OLIMEX/ESP32-POE/SOFTWARE/ARDUINO/ESP32-OTA-Ethernet-web-server/Update-progress-and-auto-recovery.jpg

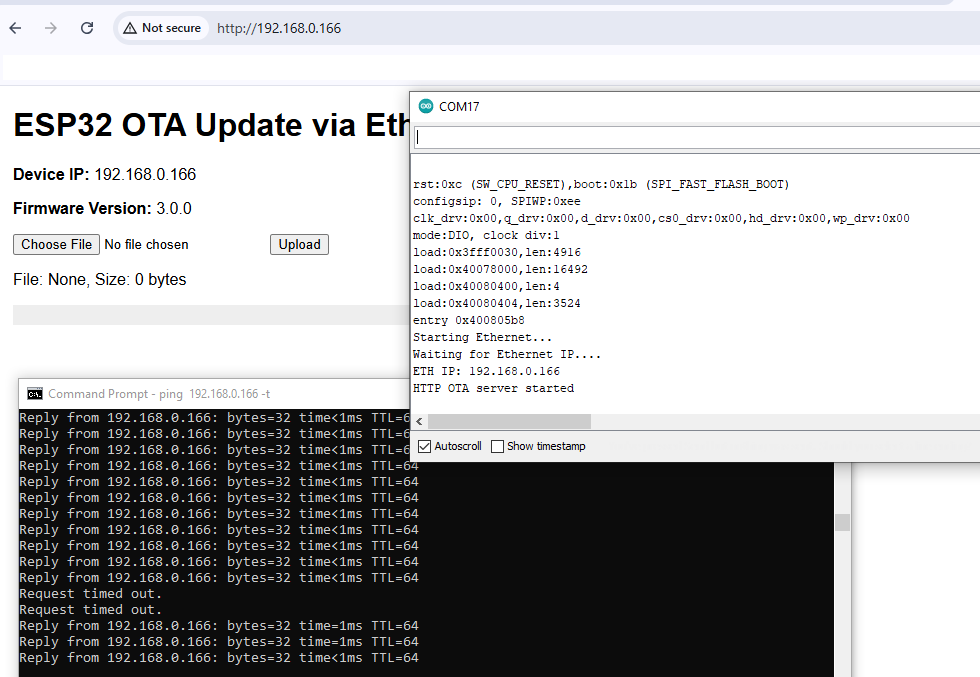
SOFTWARE/ARDUINO/ESP32-OTA-Ethernet-web-server/Update-progress-and-auto-recovery.jpg
