OLIMEX/ESP32-POE/HARDWARE/ESP32-PoE-hardware-revision-L1/3d/Micro_SD_card.step

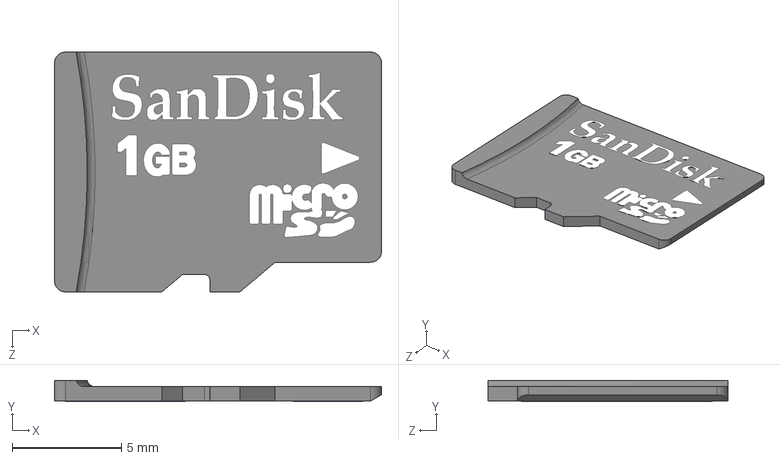
[picture p26: CAD file, 2019-03-11]
HARDWARE/ESP32-PoE-hardware-revision-L1/3d/Micro_SD_card.step
15.0 x 0.975 x 11.0 mm
