OLIMEX/ESP32-POE/HARDWARE/ESP32-PoE-hardware-revision-D/3d/CD32_inductor.step

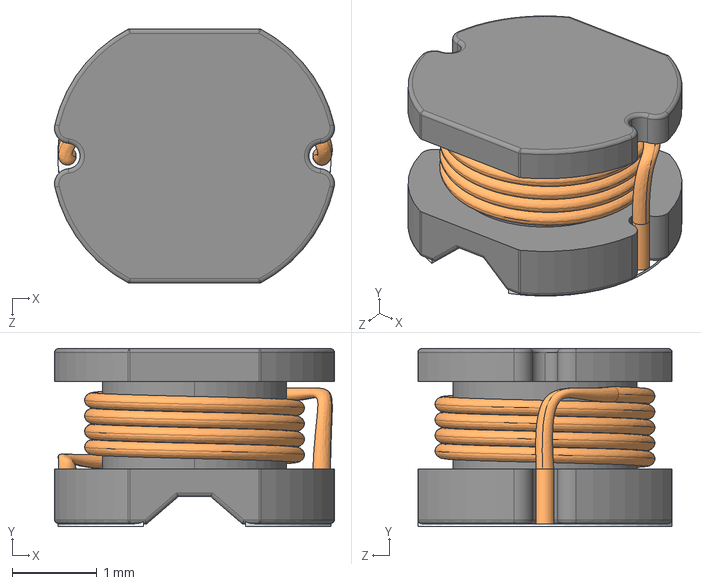
[picture p27: CAD file, 2019-03-11, an earlier design]
HARDWARE/ESP32-PoE-hardware-revision-D/3d/CD32_inductor.step
3.30 x 2.10 x 3.00 mm
