OLIMEX/ESP32-POE/SOFTWARE/ARDUINO/ESP32-BME280-WEB/ESP32-BME280-advanced/example-result.jpg

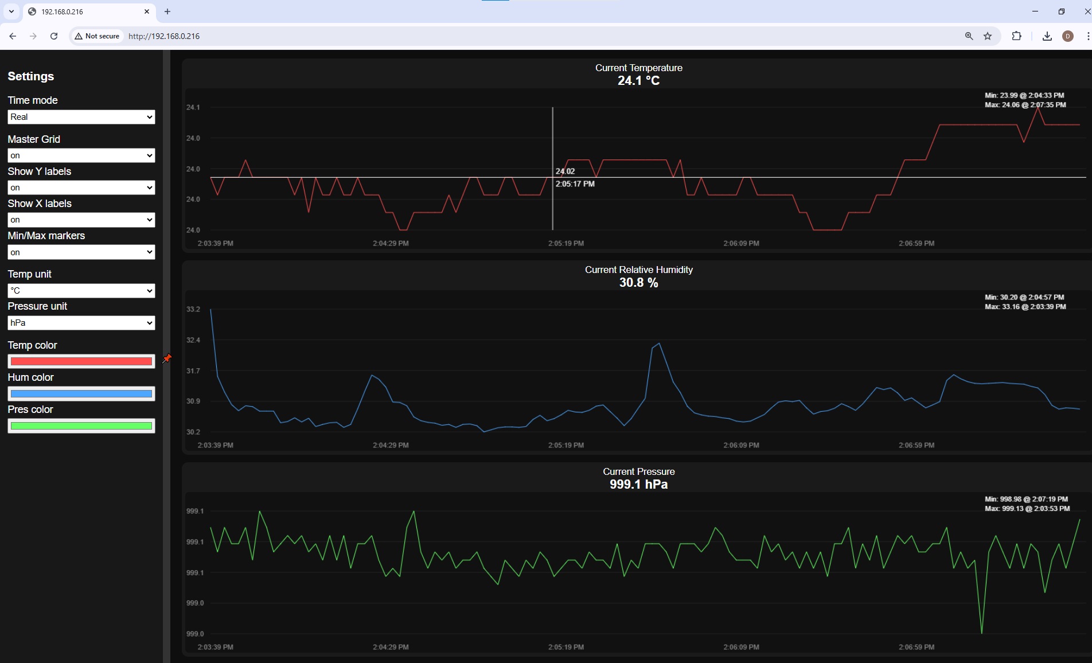
SOFTWARE/ARDUINO/ESP32-BME280-WEB/ESP32-BME280-advanced/example-result.jpg
