OLIMEX/ESP32-POE/SOFTWARE/ARDUINO/ESP32-BME280-WEB/ESP32-BME280-simple/example-result.jpg

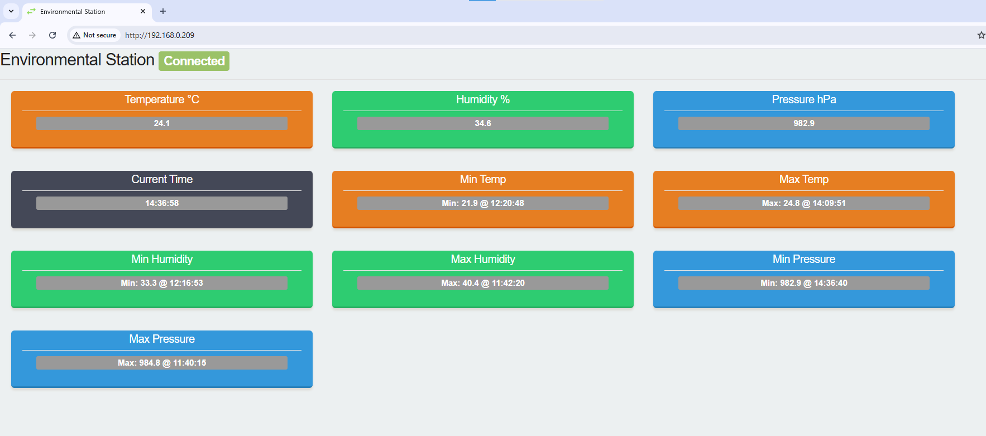
SOFTWARE/ARDUINO/ESP32-BME280-WEB/ESP32-BME280-simple/example-result.jpg
