OLIMEX/ESP32-POE/HARDWARE/ESP32-PoE-hardware-revision-J/ESP32-PoE_Rev_J.pdf

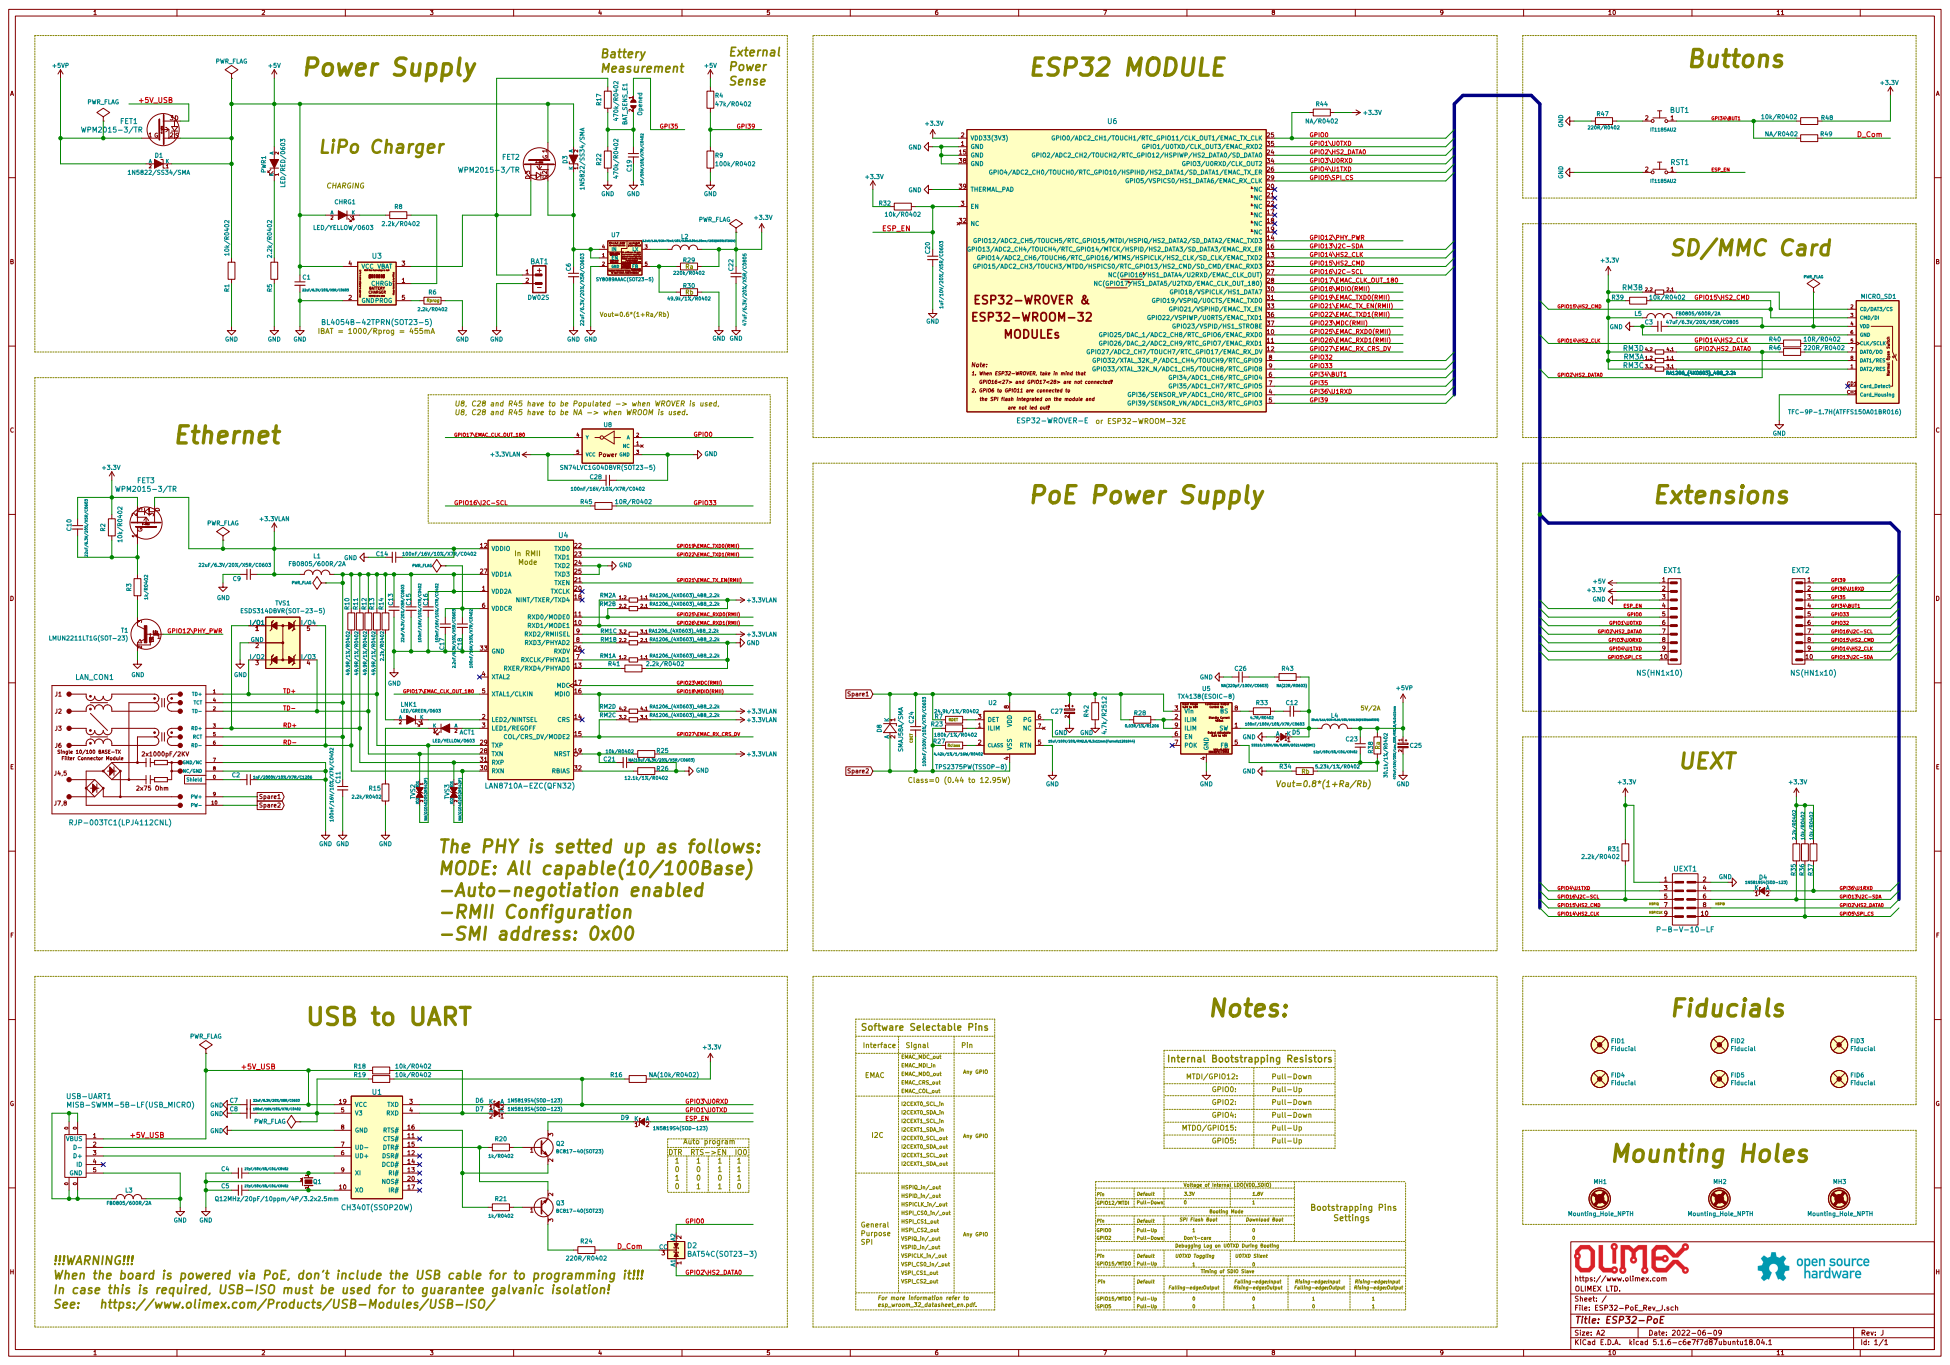
[picture p48: page 1]
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

load current capability! Lx=2.2uH
Cout=2x22uF/6.3V/X5R DCR<50mR

SD/MMC Card Ra Rb
GPIO15\HS2_CMD GPIO16\I2C-SCL GPIO13\I2C-SDA

Vout=0.6*(1+Ra/Rb) EN 1 GND 2

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

1. 1. 1. When ESP32-WROVER, take in mind that

GPIO16<27> and GPIO17<28> are not connected! MODULEs

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

4 RTN 5 PG 6 NC VDD 7 8U2 TPS2375PW(TSSOP-8) C15 100nF/16V/10%/X7R/C0402

2 D8 SMAJ58A/SMA IO11 IO22TVS3 NA(GG0402052R542P) IO11 IO22TVS2 NA(GG0402052R542P) GND

4 FB 5 EN 6 POK 7 BS 8

1 2 C25 470uF/10V/20%/Low_ESR/RM2.5/6.0x11mm ILIM 1 CLASS 2 DET 3 VSS

Default Default USB to UART

EMAC_MDC_out EMAC_MDI_in EMAC_MDO_out EMAC_CRS_out !!!WARNING!!! When the board is powered via PoE, don't include the USB cable for to programming it!!!

0 Falling-edge:Input GPIO15/MTDO

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

File: ESP32-PoE_Rev_J.sch Sheet: / OLIMEX LTD. https://www.olimex.com
