OLIMEX/ESP32-POE/HARDWARE/ESP32-PoE-hardware-revision-I/ESP32-PoE_Rev_I_BOM.pdf

ESP32-PoE_Rev_I_BOM | 12/23/2021

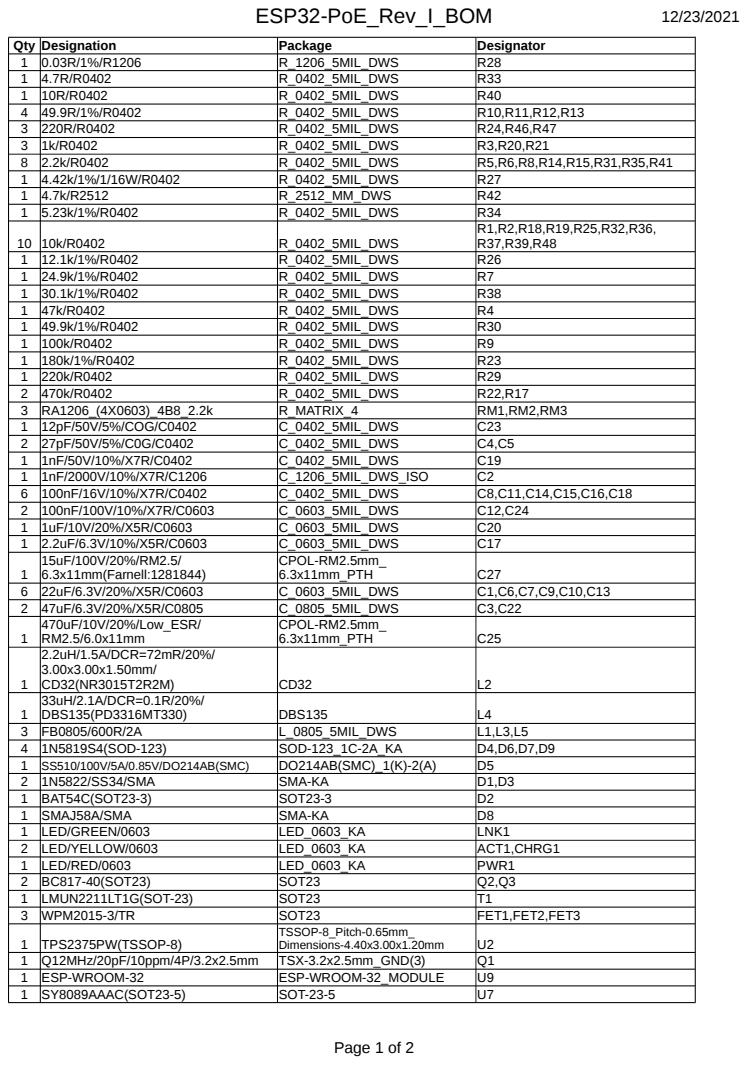
[picture p49: page 1]

ESP32-PoE_Rev_I_BOM | 12/23/2021
1 LAN8710A-EZC(QFN32) | | U4
1 BL4054B-42TPRN(SOT23-5) | SOT-23-5 | U3
1 CH340T(SSOP20W) | SSOP-20W | U1
1 TX4138(ESOIC-8) | ESOIC-8 | U5
1 ESDS314DBVR(SOT-23-5) | SOT-23-5 | TVS1
1 TFC-9P-1.7H(ATFFS150A01BR016) | | MICRO_SD1
1 RJP-003TC1(LPJ4112CNL) | RJP-003TC1(LPJ4112CNL) | LAN_CON1
1 DW02R | LIPO_BAT-CON2DW02R | BAT1
1 MISB-SWMM-5B-LF(USB_MICRO) | USB-MICRO_MISB-SWMM-5B_LF USB-UART1
1 P-B-V-10-LF | GBH-254-SMT-10 | UEXT1
2 NS(HN1x10) | HN1x10 | EXT2,EXT1
2 IT1185AU2 | IT1185AU2_V2 | BUT1,RST1
1 Opened | SJ_1_SMALLER | BAT_SENS_E1
2 NA(GG0402052R542P) | D_0402_5MIL_DWS | TVS2,TVS3
1 NA(10k/R0402) | R_0402_5MIL_DWS | R16
2 NA/R0402 | R_0402_5MIL_DWS | R44,R49
1 NA(10uF/6.3V/20%/X5R/C0603) | C_0603_5MIL_DWS | C21
1 NA(22R/R0603) | R_0603_5MIL_DWS | R43
1 NA(220pF/100V/C0603) | C_0603_5MIL_DWS | C26

QFN32_EP(33)_5.00x5.00x
0.90mm_Pitch_0.50mm

uSD(TFC-9P-1.xH
(ATFFS150A01BR016))
