OLIMEX/ESP32-POE/HARDWARE/ESP32-PoE-hardware-revision-G1/ESP32-PoE_Rev_G1.pdf

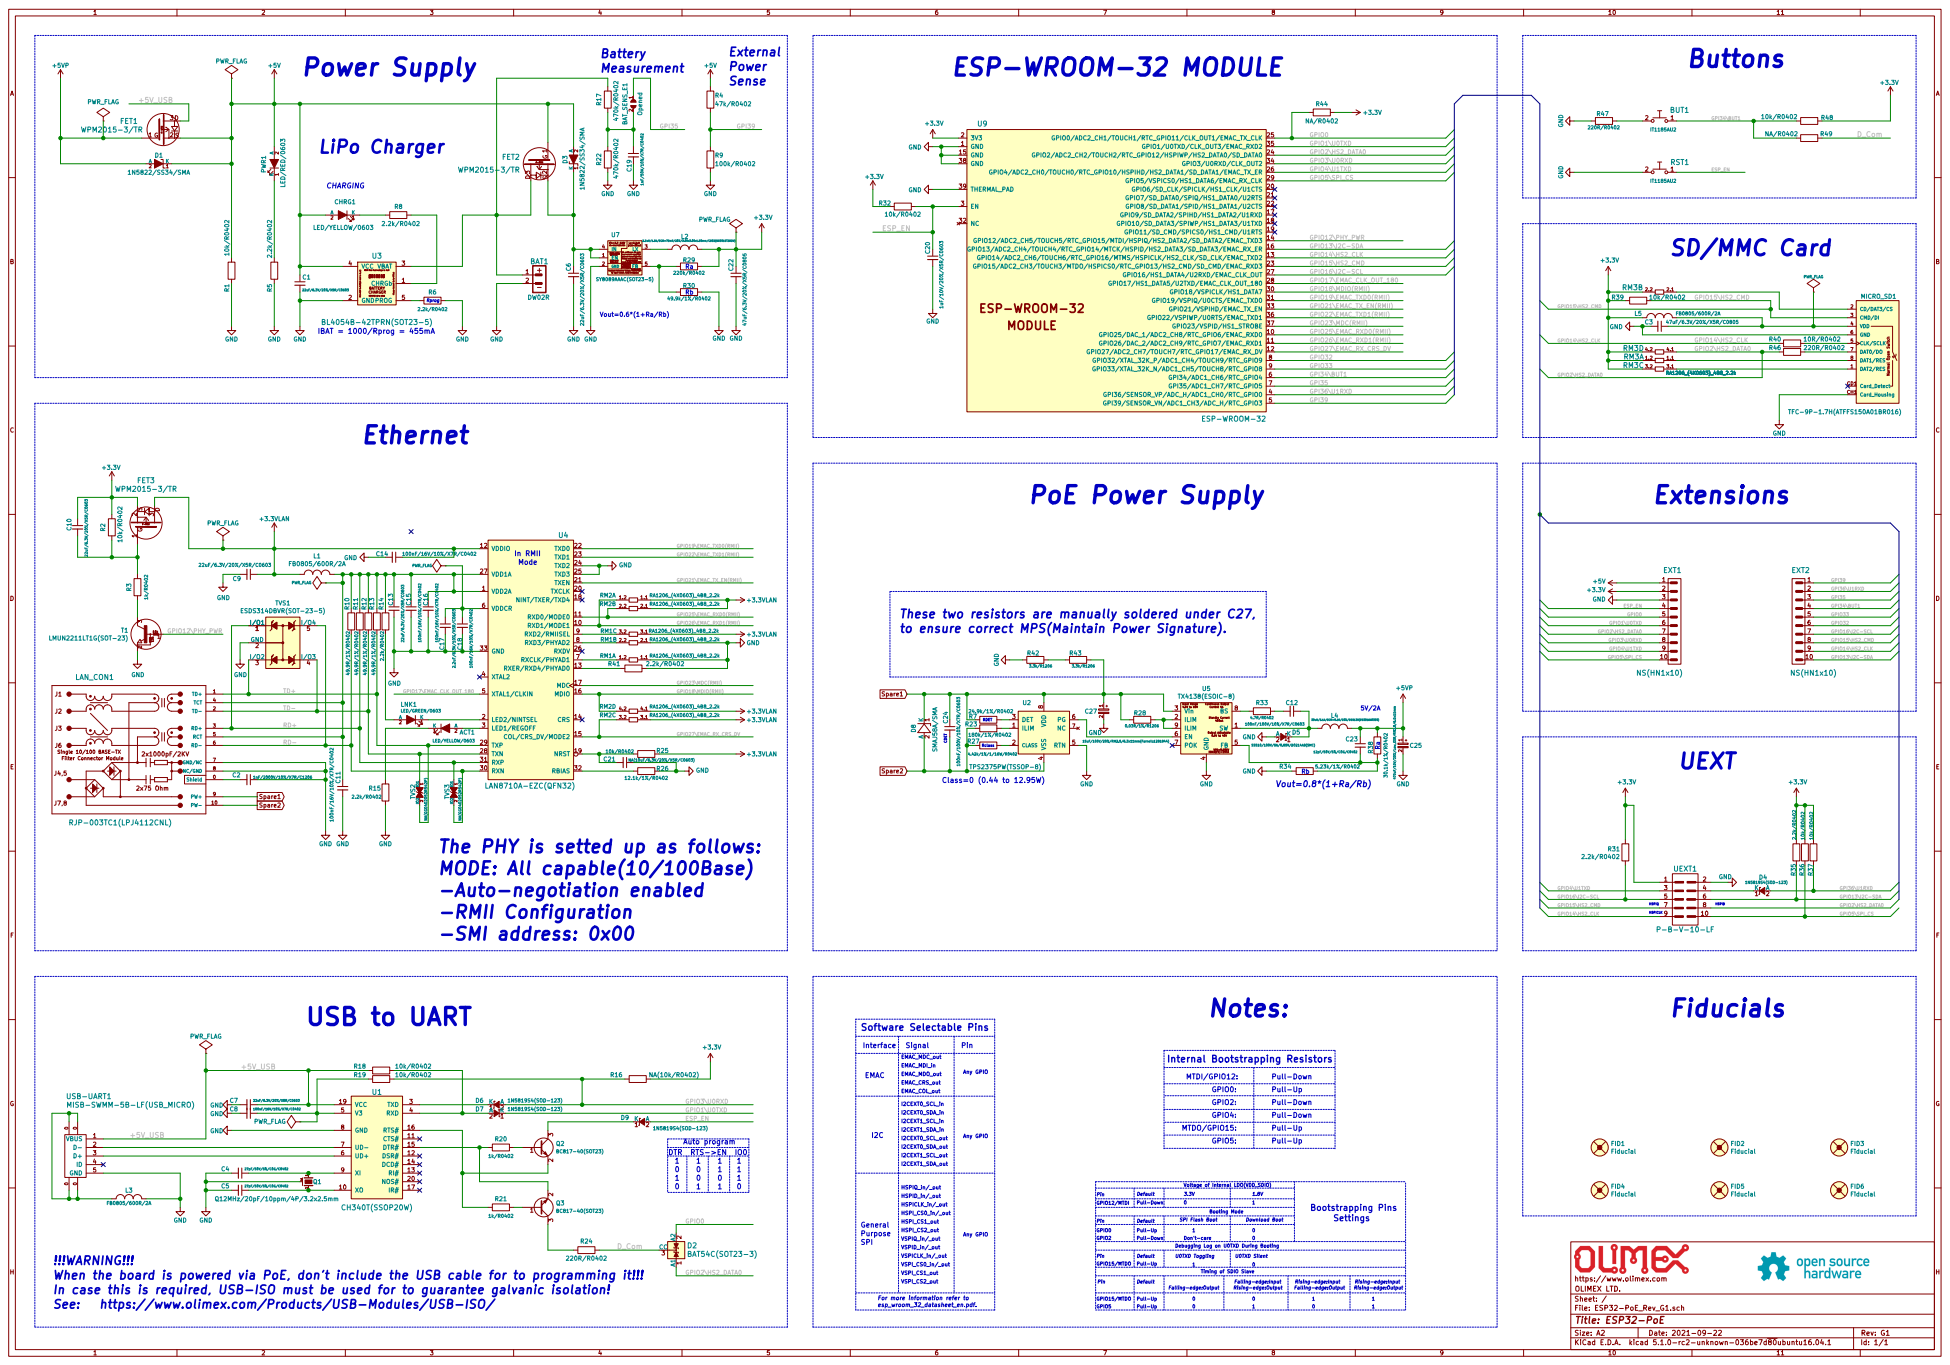
[picture p50: page 1]

load current capability! Lx=2.2uH

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

PWR_FLAG The PHY is setted up as follows:

to ensure correct MPS(Maintain Power Signature). R43

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

File: ESP32-PoE_Rev_G1.sch Sheet: / OLIMEX LTD. https://www.olimex.com
