OLIMEX/ESP32-POE/HARDWARE/ESP32-PoE-hardware-revision-G1/ESP32-PoE_Rev_G1_BOM.pdf

ESP32-PoE_Rev_G1_BOM | 11/05/2021

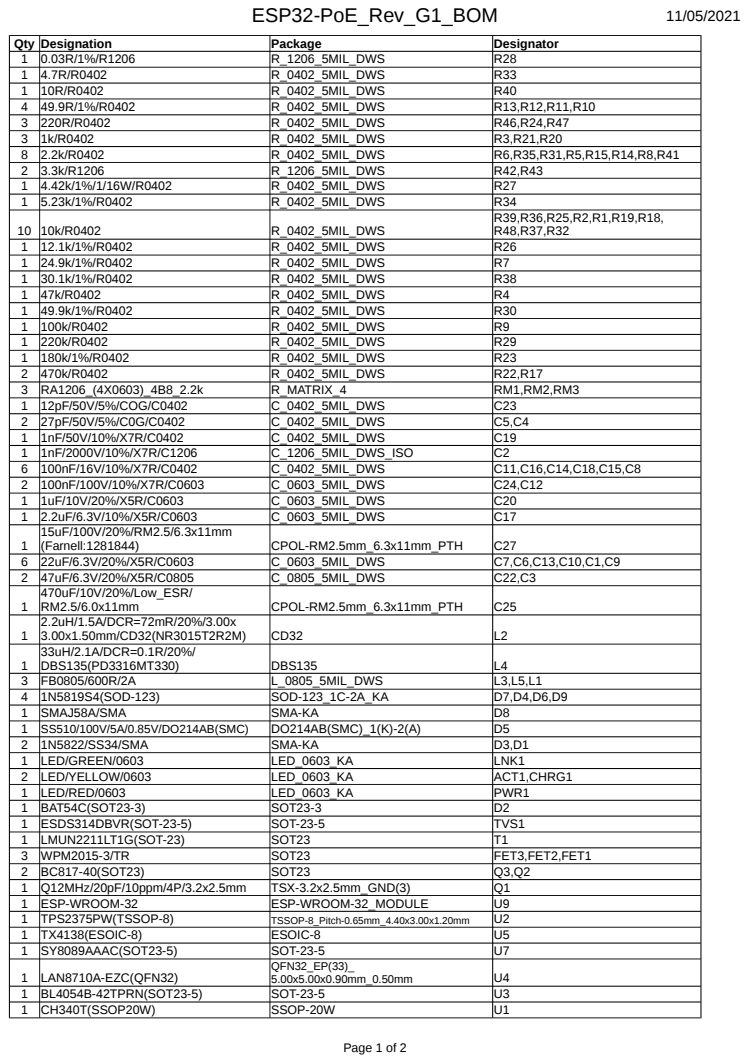
[picture p51: page 1]

ESP32-PoE_Rev_G1_BOM | 11/05/2021
1 RJP-003TC1(LPJ4112CNL) | RJP-003TC1(LPJ4112CNL) | LAN_CON1
1 DW02R | LIPO_BAT-CON2DW02R | BAT1
1 TFC-9P-1.7H(ATFFS150A01BR016) | uSD(TFC-9P-1.xH(ATFFS150A01BR016)) MICRO_SD1
1 MISB-SWMM-5B-LF(USB_MICRO) | USB-MICRO_MISB-SWMM-5B_LF | USB-UART1
1 P-B-V-10-LF | GBH-254-SMT-10 | UEXT1
2 NS(HN1x10) | HN1x10 | EXT2,EXT1
2 IT1185AU2 | IT1185AU2_V2 | BUT1,RST1
1 Opened | SJ_1_SMALLER | BAT_SENS_E1
1 NA(10k/R0402) | R_0402_5MIL_DWS | R16
2 NA(GG0402052R542P) | D_0402_5MIL_DWS | TVS2,TVS3
1 NA(10uF/6.3V/20%/X5R/C0603) | C_0603_5MIL_DWS | C21
2 NA/R0402 | R_0402_5MIL_DWS | R44,R49
