OLIMEX/ESP32-POE/HARDWARE/ESP32-PoE-hardware-revision-E/ESP32-PoE_Rev_E.pdf

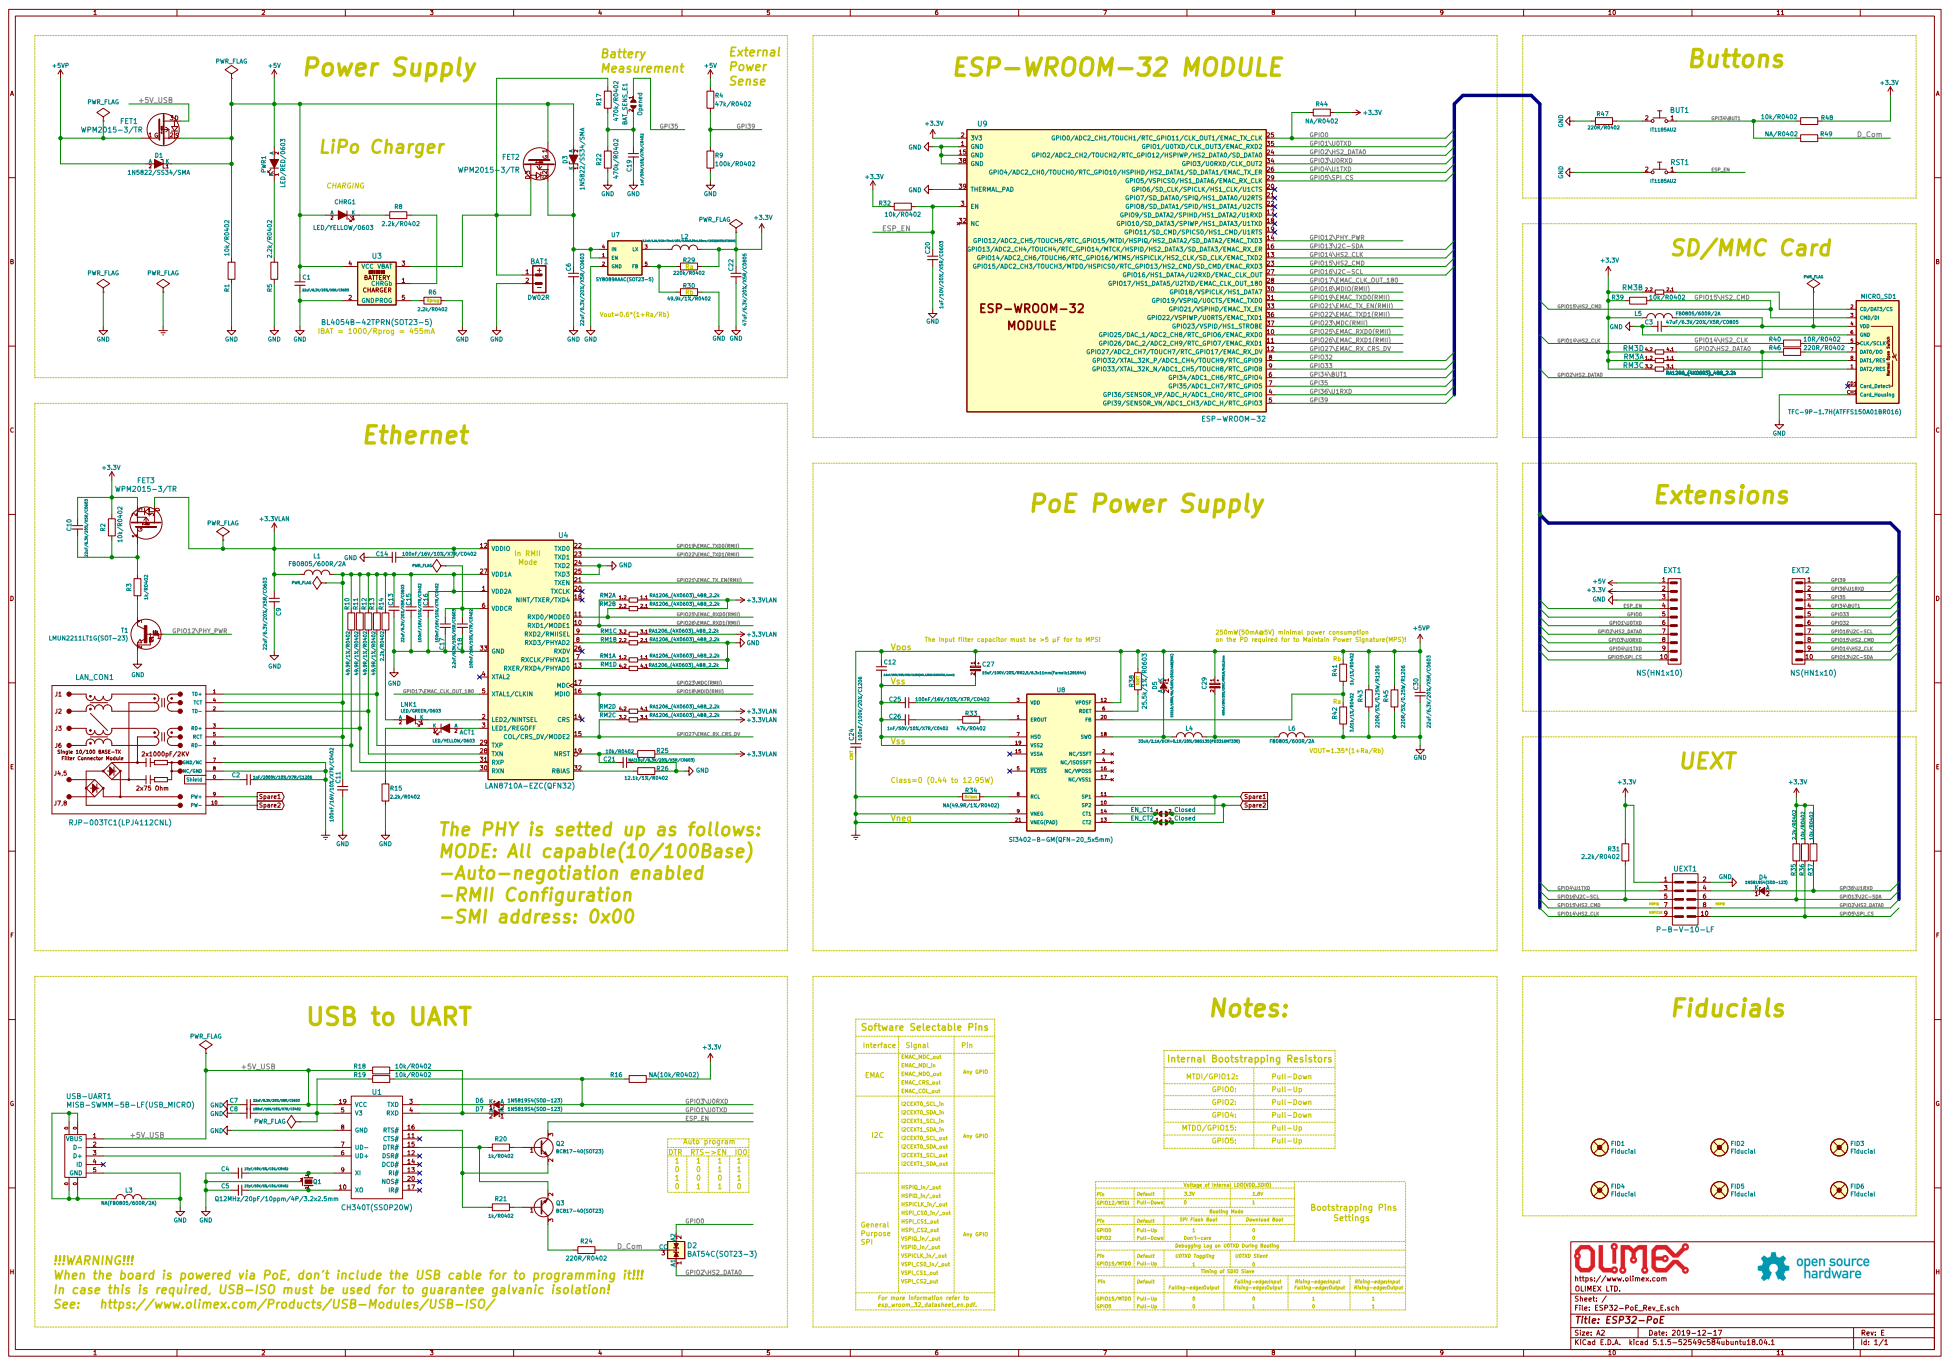
[picture p52: page 1]

GPIO18\MDIO(RMII) GPIO26\EMAC_RXD1(RMII) GPIO21\EMAC_TX_EN(RMII)

250mW(50mA@5V) minimal power consumption on the PD required for to Maintain Power Signature(MPS)!

Vss Vpos Vneg Vss

2.2k/R0402 GND
Pin The PHY is setted up as follows:
MODE: All capable(10/100Base)
-Auto-negotiation enabled
-RMII Configuration
-SMI address: 0x00

HSPIQ USB to UART

Internal Bootstrapping ResistorsBootstrapping Pins

Default Default
0 Pull-Up

0 !!!WARNING!!! When the board is powered via PoE, don't include the USB cable for to programming it!!!

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

File: ESP32-PoE_Rev_E.sch Sheet: / OLIMEX LTD. https://www.olimex.com

Rising-edge:Output Falling-edge:Input
