OLIMEX/ESP32-POE/HARDWARE/ESP32-PoE-hardware-revision-B1/ESP32-PoE_Rev_B1_BW.pdf

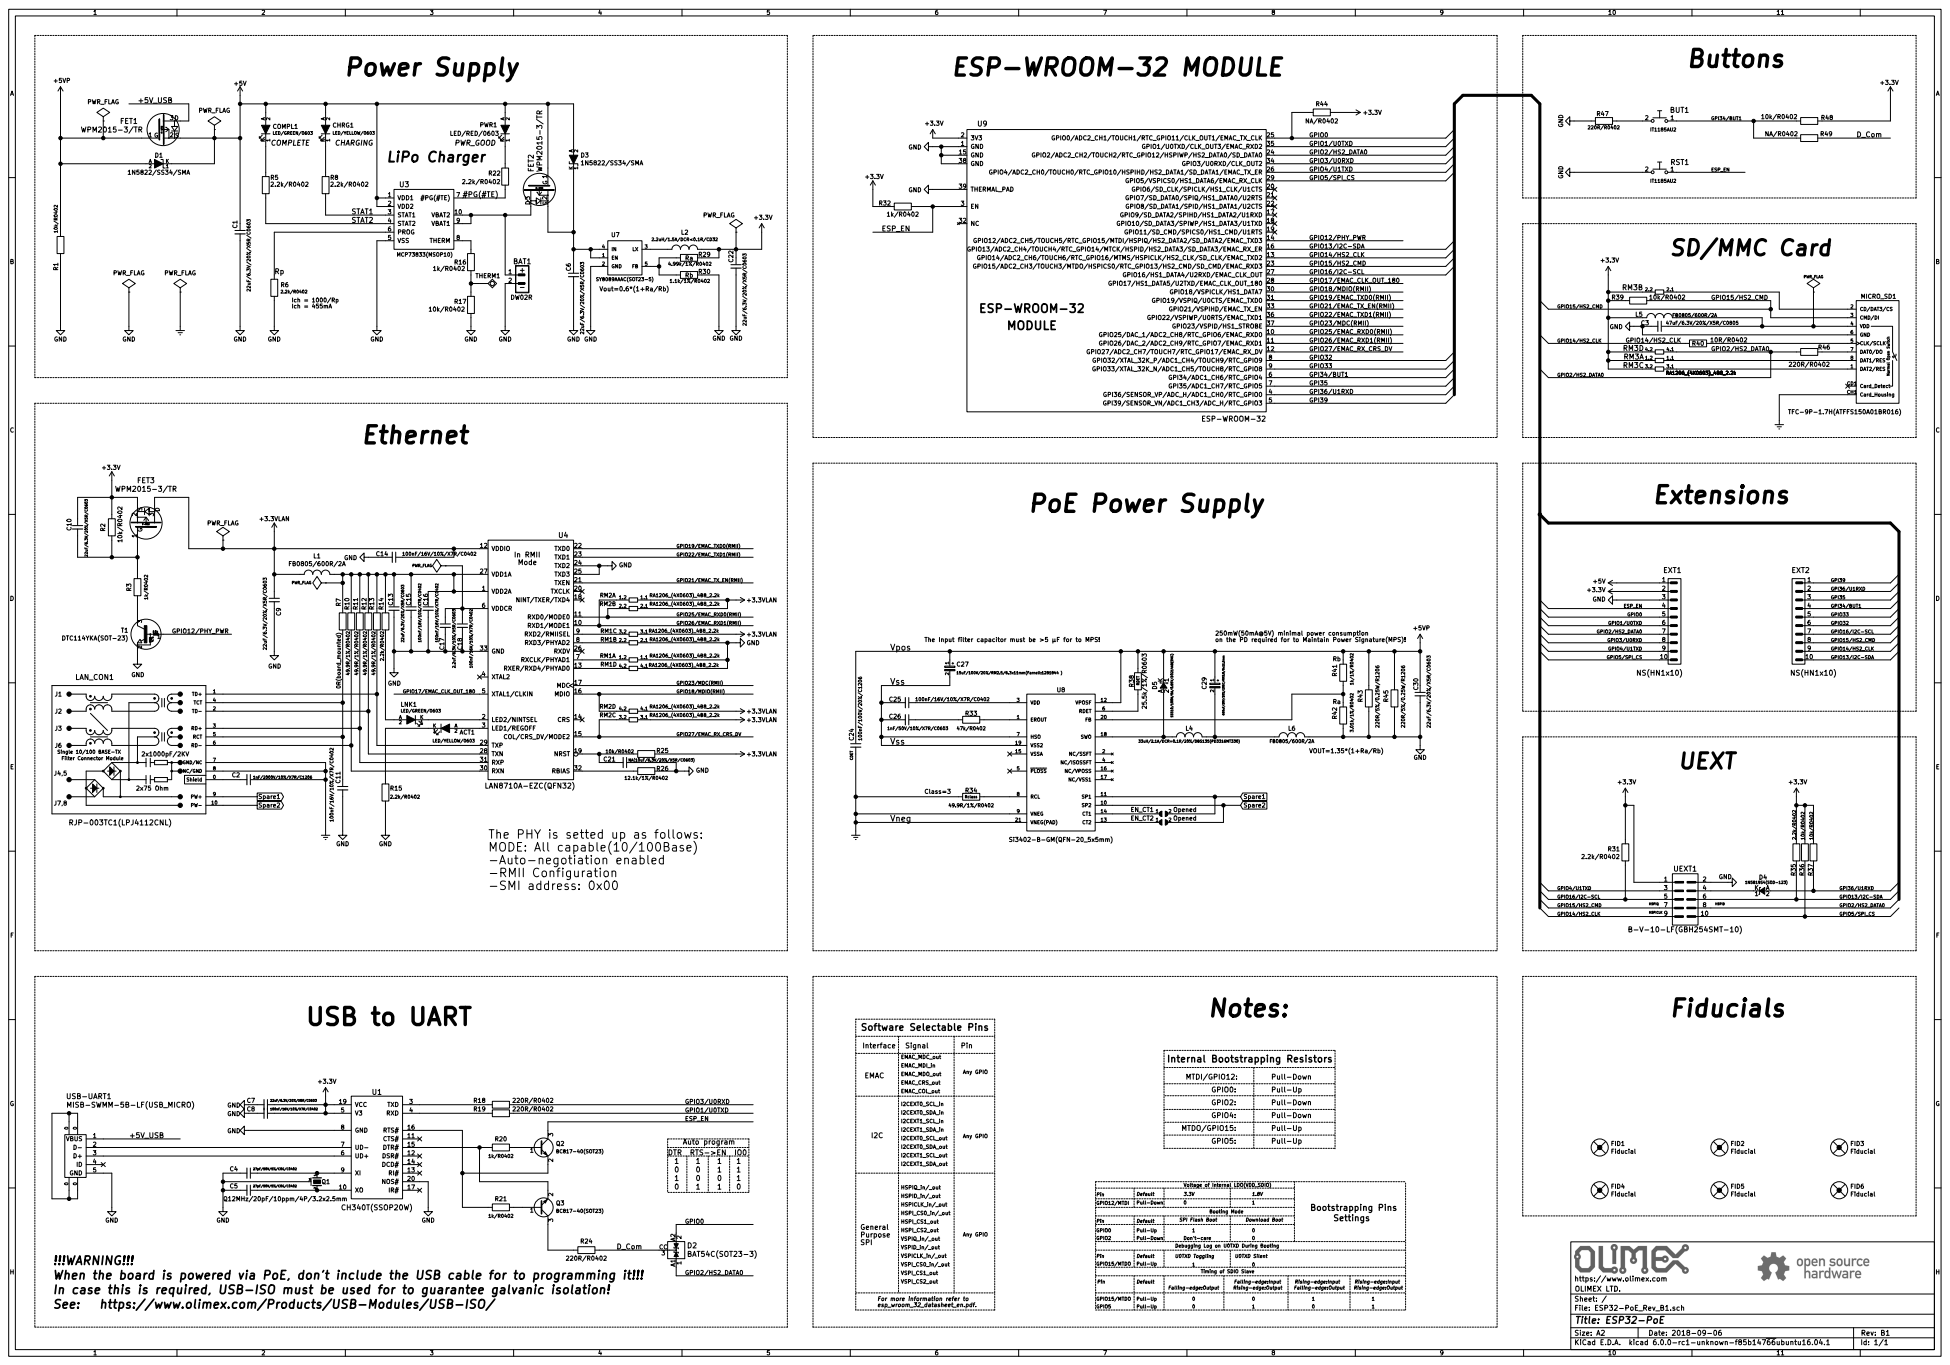
[picture p53: page 1]

PWR_FLAG The PHY is setted up as follows:

2D5 SS510/100V/5A/0.85V/DO214AB(SMC) Normal Open Switch DAT2/RES

VOUT=1.35*(1+Ra/Rb) Ra Rb Spare1

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

File: ESP32-PoE_Rev_B1.sch Sheet: / OLIMEX LTD. https://www.olimex.com
