OLIMEX/ESP32-POE/HARDWARE/ESP32-PoE-hardware-revision-B2/ESP32-PoE_Rev_B2-BOM.pdf

ESP32-PoE_Rev_B2 | 09/11/2018

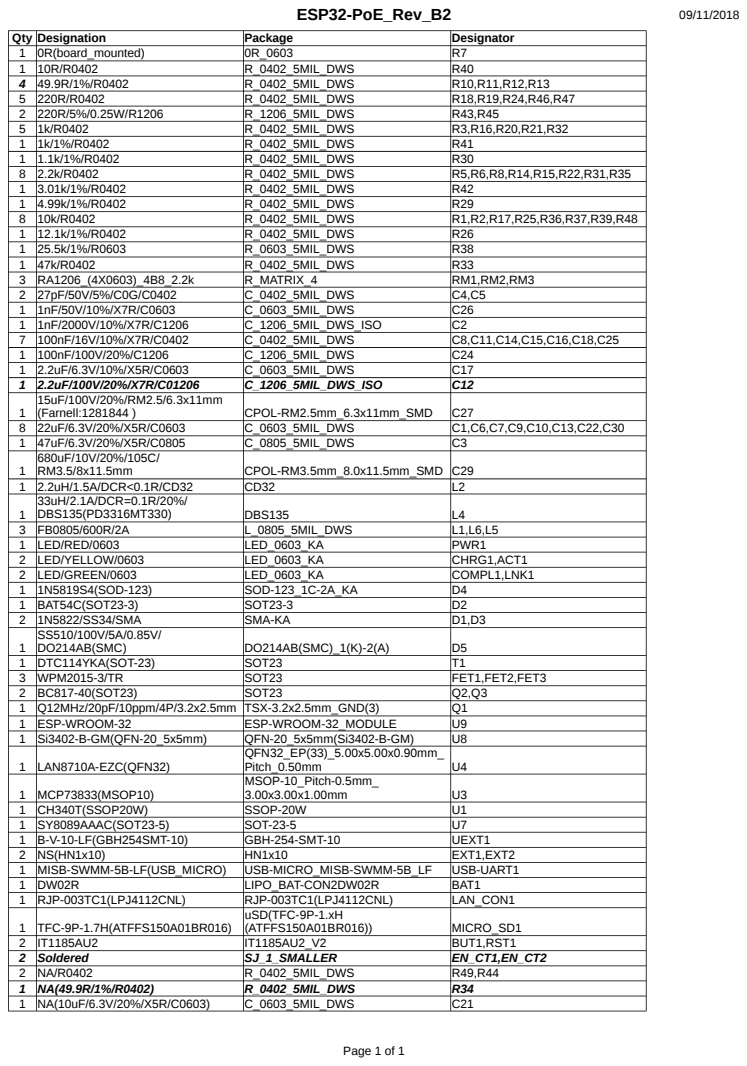
[picture p54: page 1]
