OLIMEX/ESP32-POE/HARDWARE/ESP32-PoE-hardware-revision-C1/ESP32-PoE_Rev_C_Bom.pdf

ESP32-PoE_Rev_C | 09/25/2018

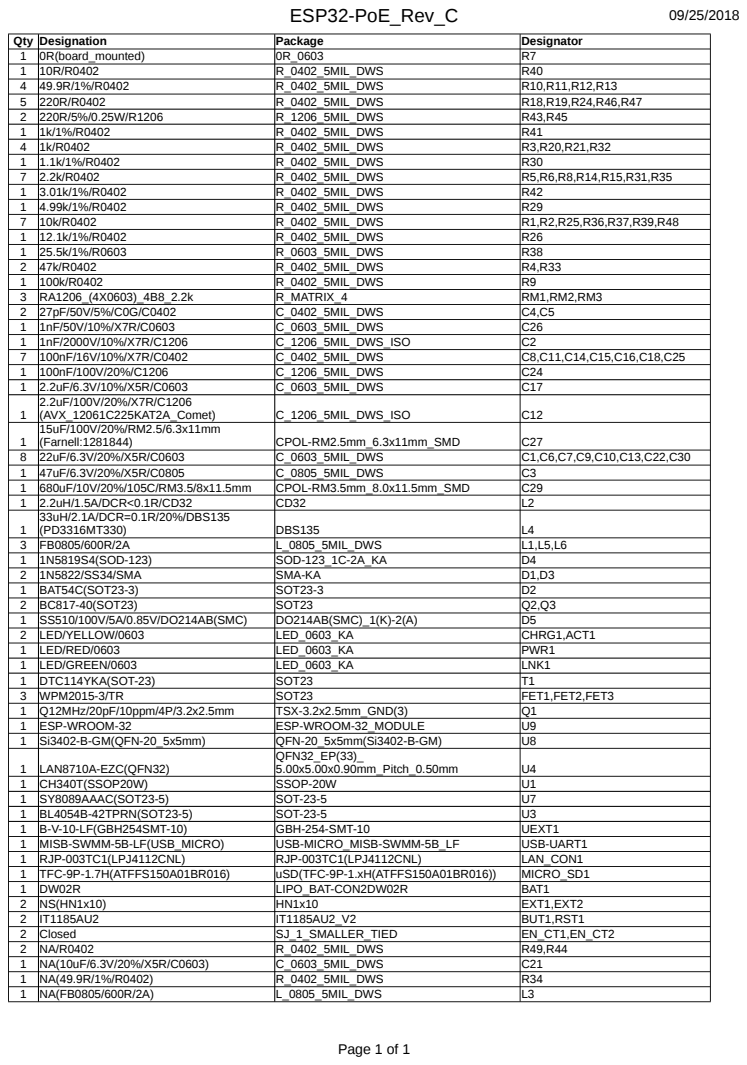
[picture p55: page 1]
