OLIMEX/ESP32-POE/HARDWARE/ESP32-PoE-hardware-revision-B1/ESP32-PoE_Rev_B1-BOM.pdf

ESP32-PoE_Rev_B1 | 09/06/2018

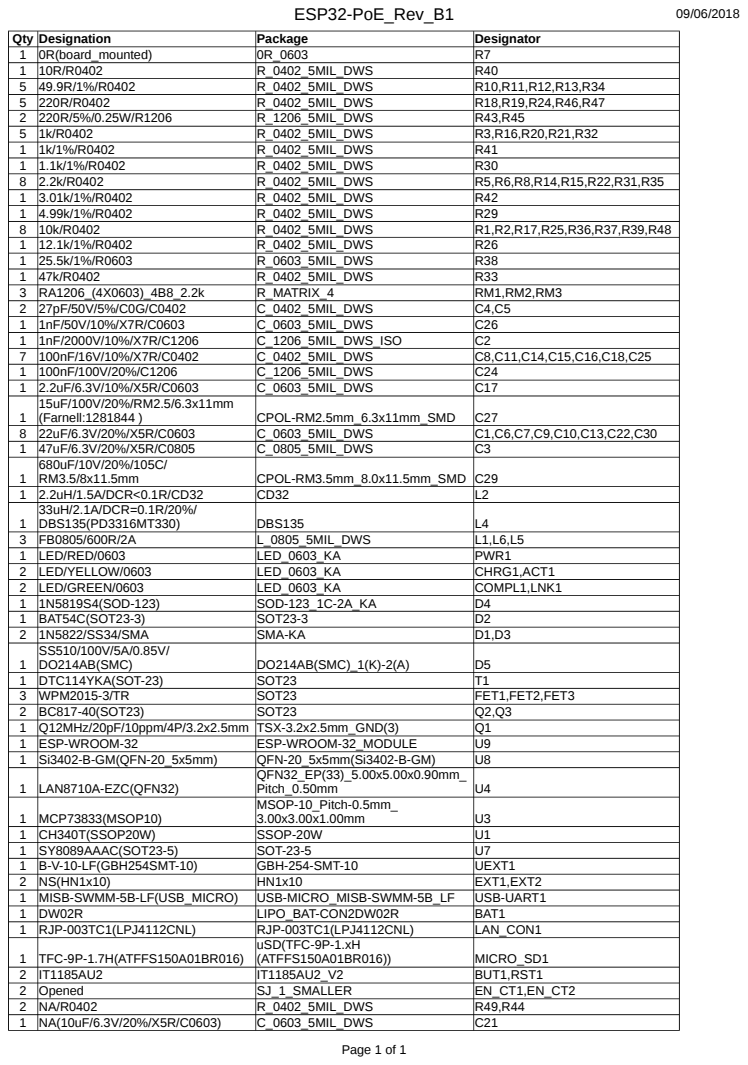
[picture p56: page 1]
